i-decosmis/CloserPlayerTRPG/other/images/20.png

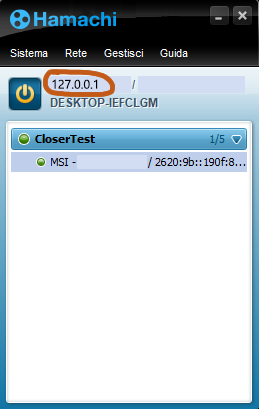
other/images/20.png
